stivberberi/capstone/src/components/custom_button/custom_button.c

#include "custom_button.h"
#include "esp_log.h"
#include "iot_button.h"

const static char *TAG = "Button"; // used as the tag for ESP_LOG's

button_handle_t setup_button(int gpio_pin) {

  // create gpio button
  button_config_t gpio_btn_cfg = {
      .type = BUTTON_TYPE_GPIO,
      .long_press_time = CONFIG_BUTTON_LONG_PRESS_TIME_MS,
      .short_press_time = CONFIG_BUTTON_SHORT_PRESS_TIME_MS,
      .gpio_button_config =
          {
              .gpio_num = gpio_pin,
              .active_level = 0,
          },
  };
  button_handle_t gpio_btn = iot_button_create(&gpio_btn_cfg);
  if (NULL == gpio_btn) {
    ESP_LOGE(TAG, "Button create failed");
  }
  return gpio_btn;
}
